meltanrm/Cable-Robot/Stl_files/Final_frame/UpperConnect_finalShortBeam.stl

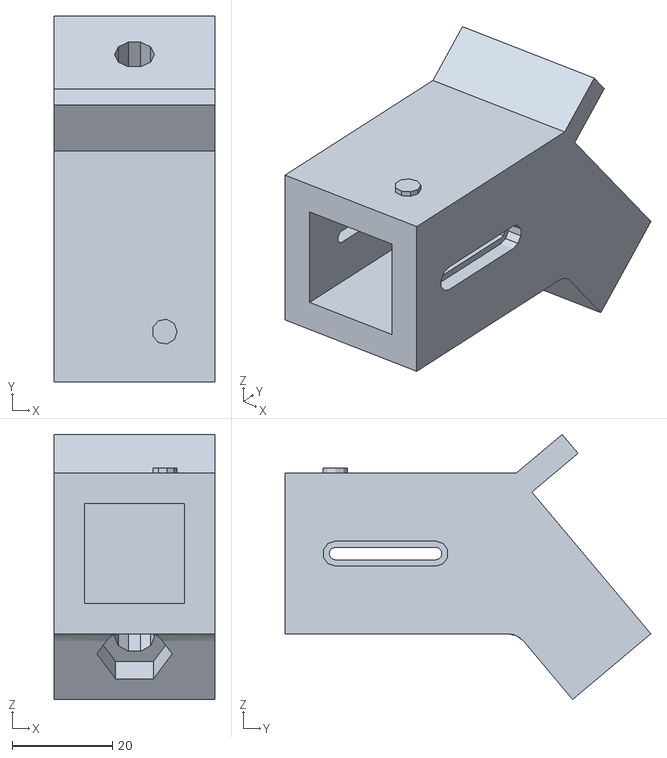
[picture p15: CAD file, 2022-04-02]
Stl_files/Final_frame/UpperConnect_finalShortBeam.stl
32.0 x 72.9 x 52.8
