meltanrm/Cable-Robot/Stl_files/Final_frame/DiagonalBeamBracket_2.stl

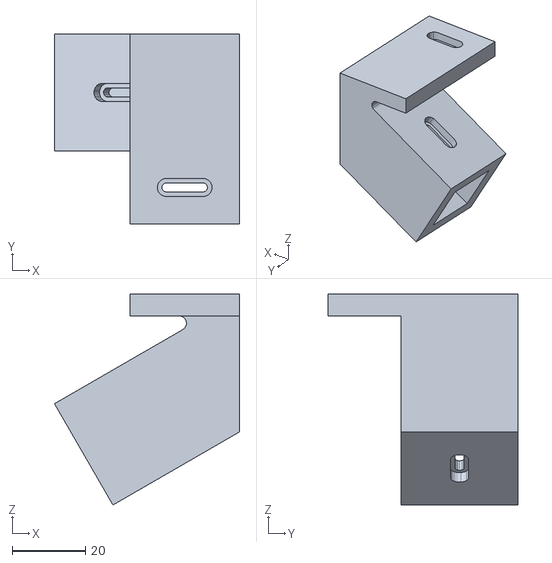
[picture p16: CAD file, 2022-04-02]
Stl_files/Final_frame/DiagonalBeamBracket_2.stl
50.6 x 52.0 x 57.7
