meltanrm/Cable-Robot/Stl_files/Final_frame/DiagonalBeamBracket.stl

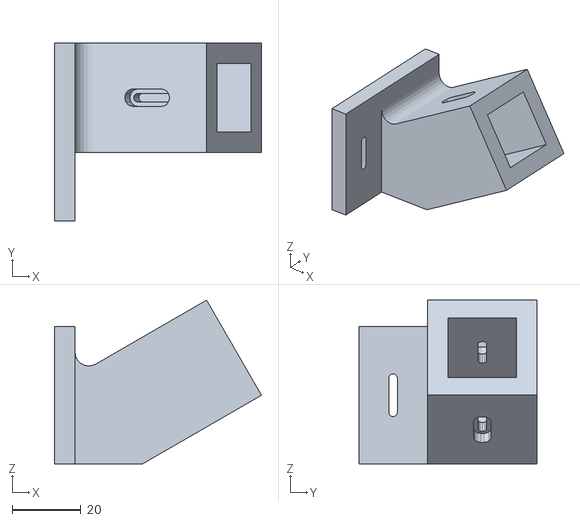
[picture p17: CAD file, 2022-04-02]
Stl_files/Final_frame/DiagonalBeamBracket.stl
60.3 x 52.0 x 47.7
