meltanrm/Cable-Robot/Stl_files/Final_frame/UpperConnect_final.stl

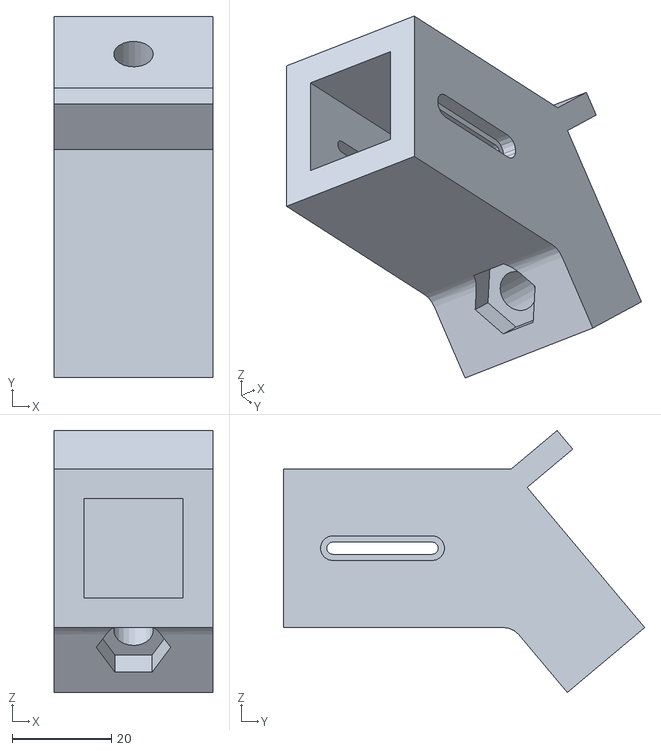
[picture p18: CAD file, 2022-04-02]
Stl_files/Final_frame/UpperConnect_final.stl
32.0 x 72.9 x 52.8
